kiu/netmeter/pics/netmeter_horzontal.jpg

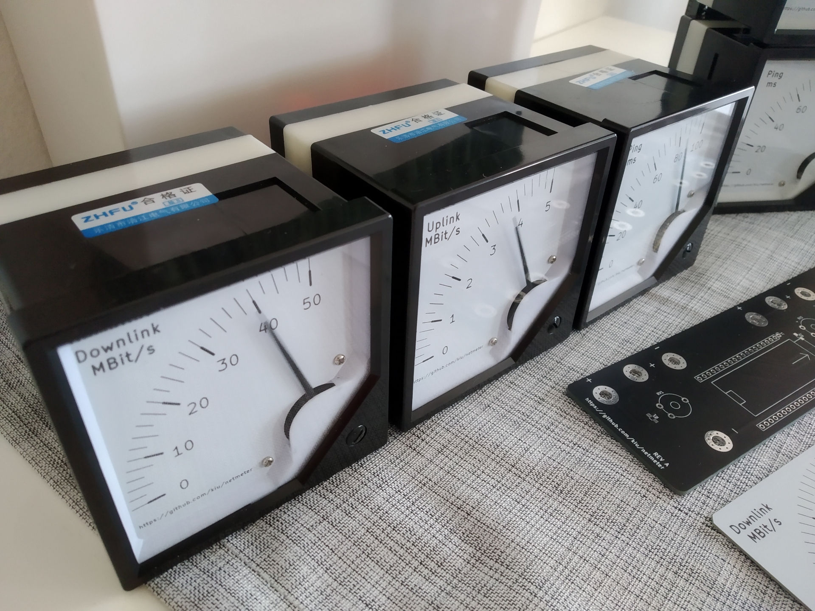
pics/netmeter_horzontal.jpg
