kiu/netmeter/pics/netmeter_two.jpg

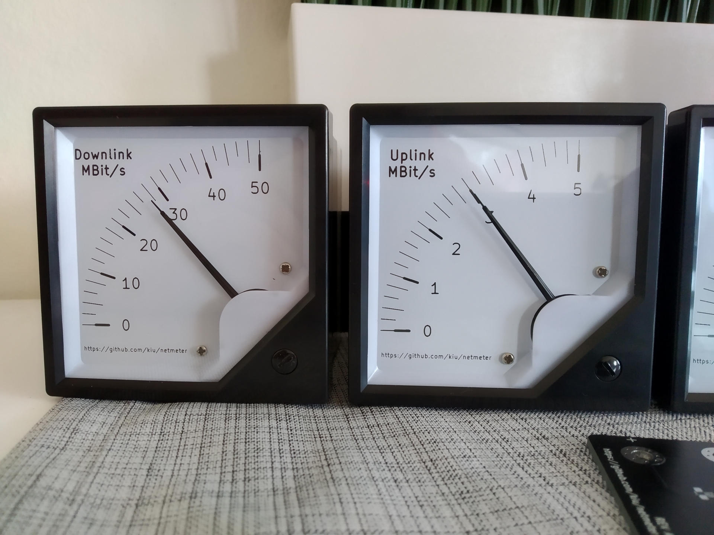
pics/netmeter_two.jpg
