kiu/netmeter/pics/netmeter_vertical_back.jpg

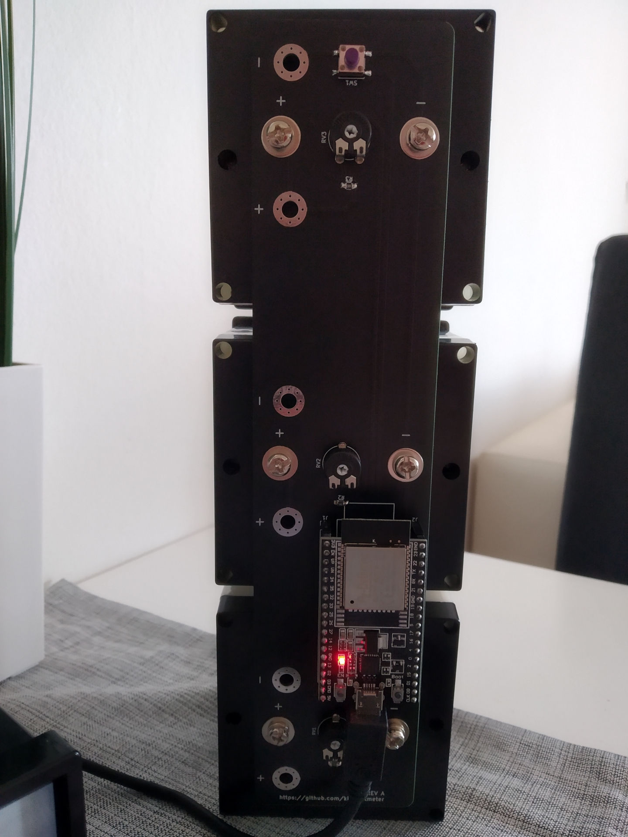
pics/netmeter_vertical_back.jpg
