kiu/netmeter/pics/org/IMG_20200919_131107.jpg

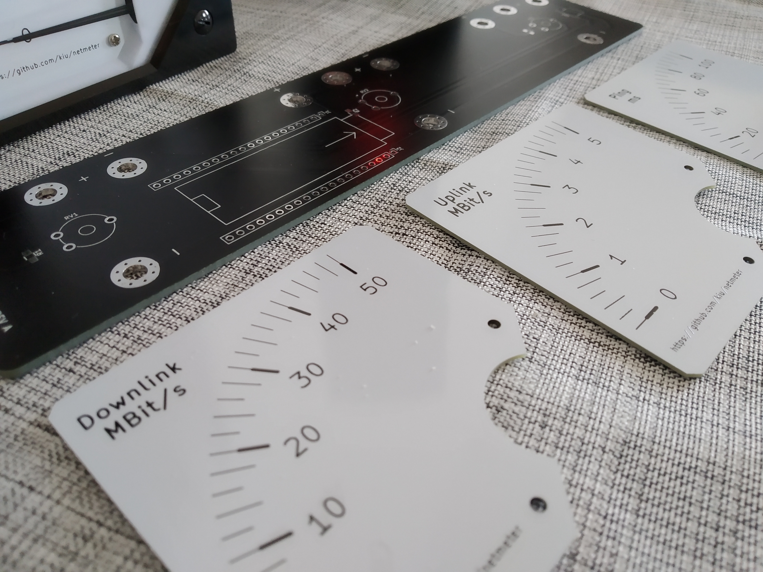
pics/org/IMG_20200919_131107.jpg
