kiu/netmeter/pics/org/IMG_20200919_131151.jpg

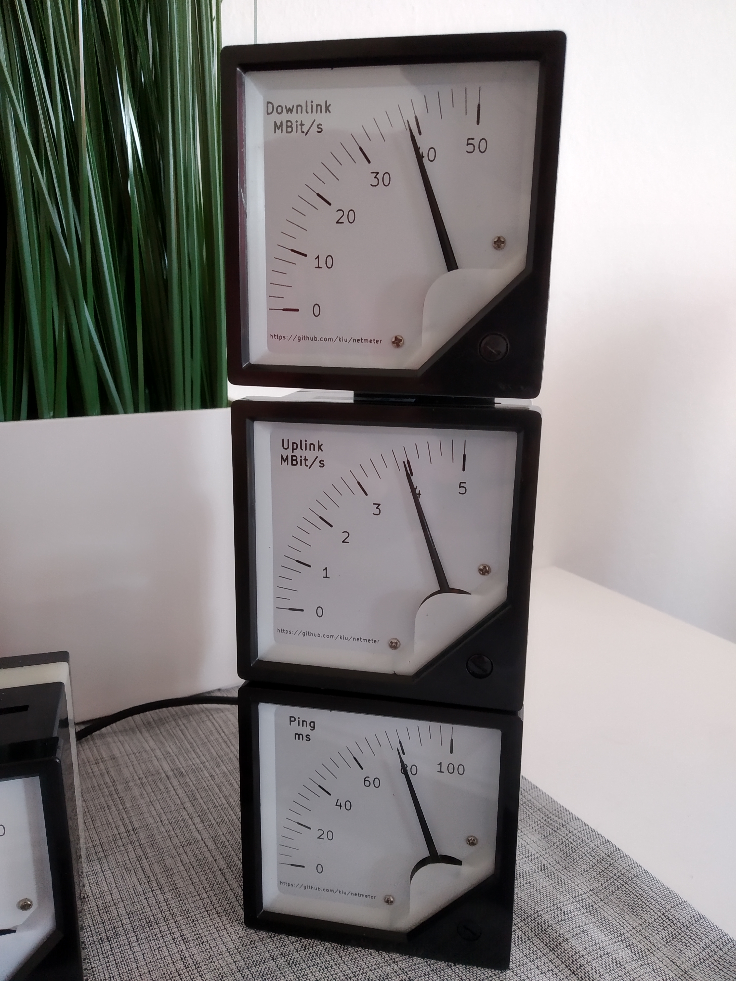
pics/org/IMG_20200919_131151.jpg
