kiu/netmeter/pics/netmeter_parts.jpg

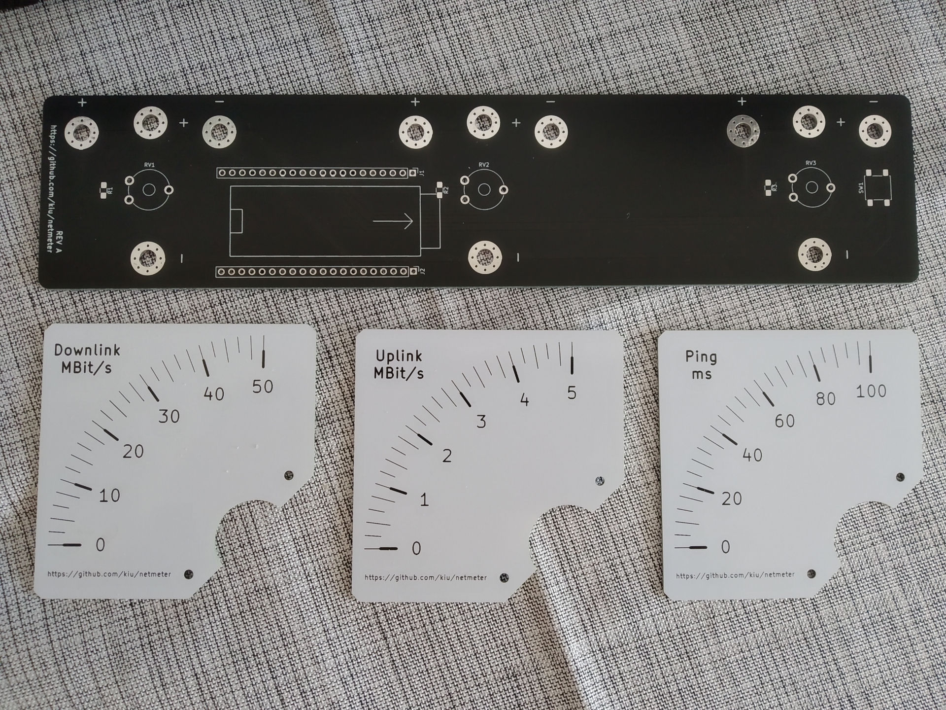
pics/netmeter_parts.jpg
